PeakeElectronicInnovation/modbus-io-system/modbus-io-controller/src/io_core/dashboard_config.h

#pragma once

#include "../sys_init.h"
#include "board_config.h"

// LittleFS configuration
#define DASHBOARD_CONFIG_FILENAME "/dashboard_config.json"
#define DASHBOARD_CONFIG_MAGIC_NUMBER 0x67

// Maximum dashboard items (64 channels = 8 boards × 8 channels)
#define MAX_DASHBOARD_ITEMS 64

// Dashboard item structure
struct DashboardItem {
    uint8_t boardIndex;
    uint8_t channelIndex;
    uint8_t displayOrder;
    bool showInChart;
};

// Dashboard configuration structure
struct DashboardConfig {
    uint8_t itemCount;
    bool chartVisible;
    uint8_t chartItemCount;
    DashboardItem items[MAX_DASHBOARD_ITEMS]; // Maximum dashboard items (80 channels)
};

// Dashboard configuration manager APIs
void init_dashboard_config(void);
bool loadDashboardConfig(void);
bool saveDashboardConfig(void);
void setupDashboardAPI(void);

// API handlers
void handleGetDashboardItems(void);
void handleSaveDashboardOrder(void);

// Dashboard management functions
bool addDashboardItem(uint8_t boardIndex, uint8_t channelIndex);
bool removeDashboardItem(uint8_t boardIndex, uint8_t channelIndex);
bool updateDashboardOrder(uint8_t *boardIndices, uint8_t *channelIndices, uint8_t *displayOrders, uint8_t count);
bool updateDashboardOrderWithChart(uint8_t *boardIndices, uint8_t *channelIndices, uint8_t *displayOrders, bool *showInChart, uint8_t count);

// Global variables
extern DashboardConfig dashboardConfig;
