PeakeElectronicInnovation/modbus-io-system/modbus-io-controller/src/io_core/board_status.h

#pragma once

#include "../sys_init.h"
#include "io_objects.h"
#include "board_config.h"

// API function declarations
void setupBoardStatusAPI(void);

// API handlers
void handleGetBoardStatus(void);
void handleGetAllBoardsStatus(void);
void handleGetThermocoupleData(void);
void handleResetAlarm(void);
void handleResetAllAlarms(void);
